wladwnt/CAN-Gateway/img/img_z1.jpg

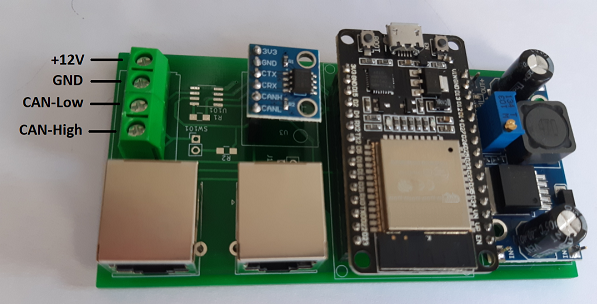
img/img_z1.jpg
