wladwnt/CAN-Gateway/img/knxip_set_en.jpg

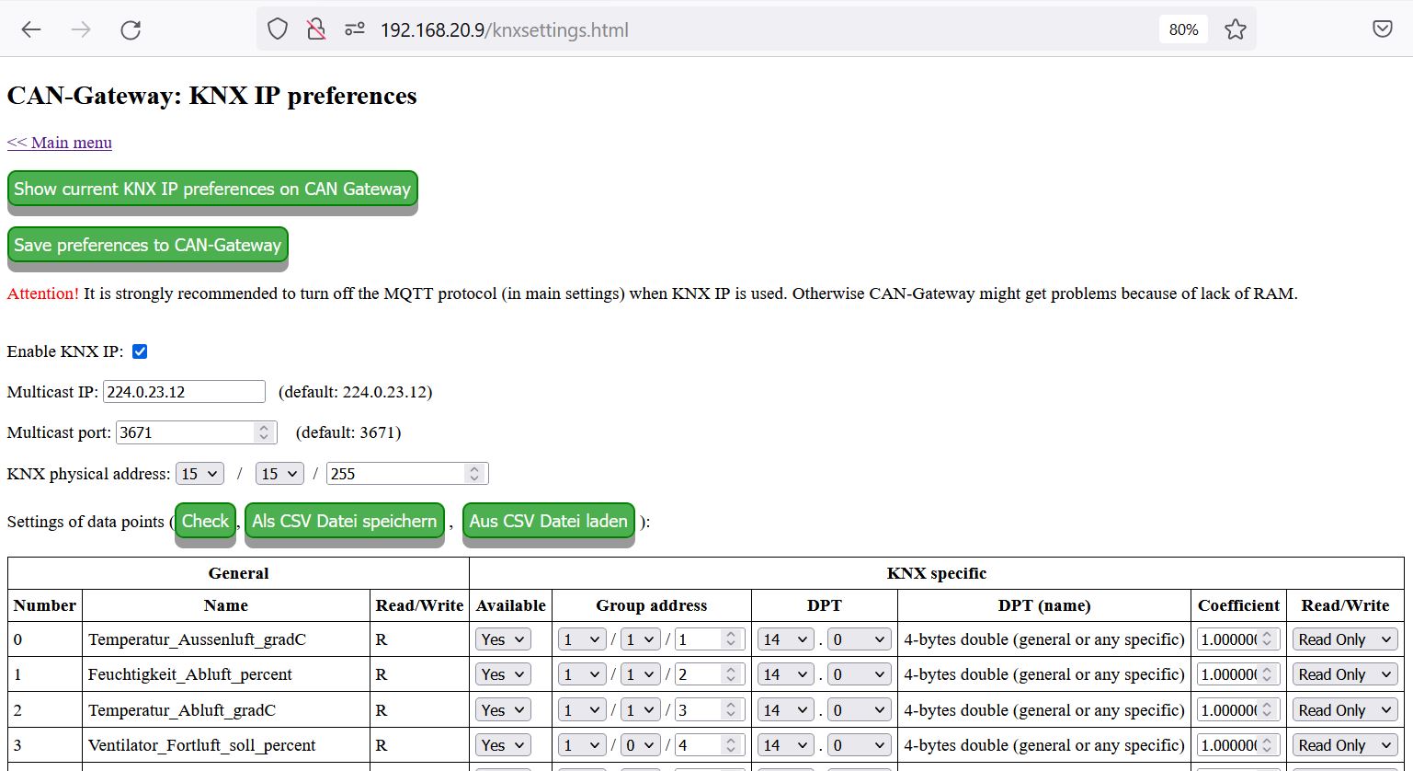
img/knxip_set_en.jpg
